foostan/lskbd/pcbs/common/left.kicad_sch

## KiCad design pcbs/common/left.kicad_sch (2024-03-01)

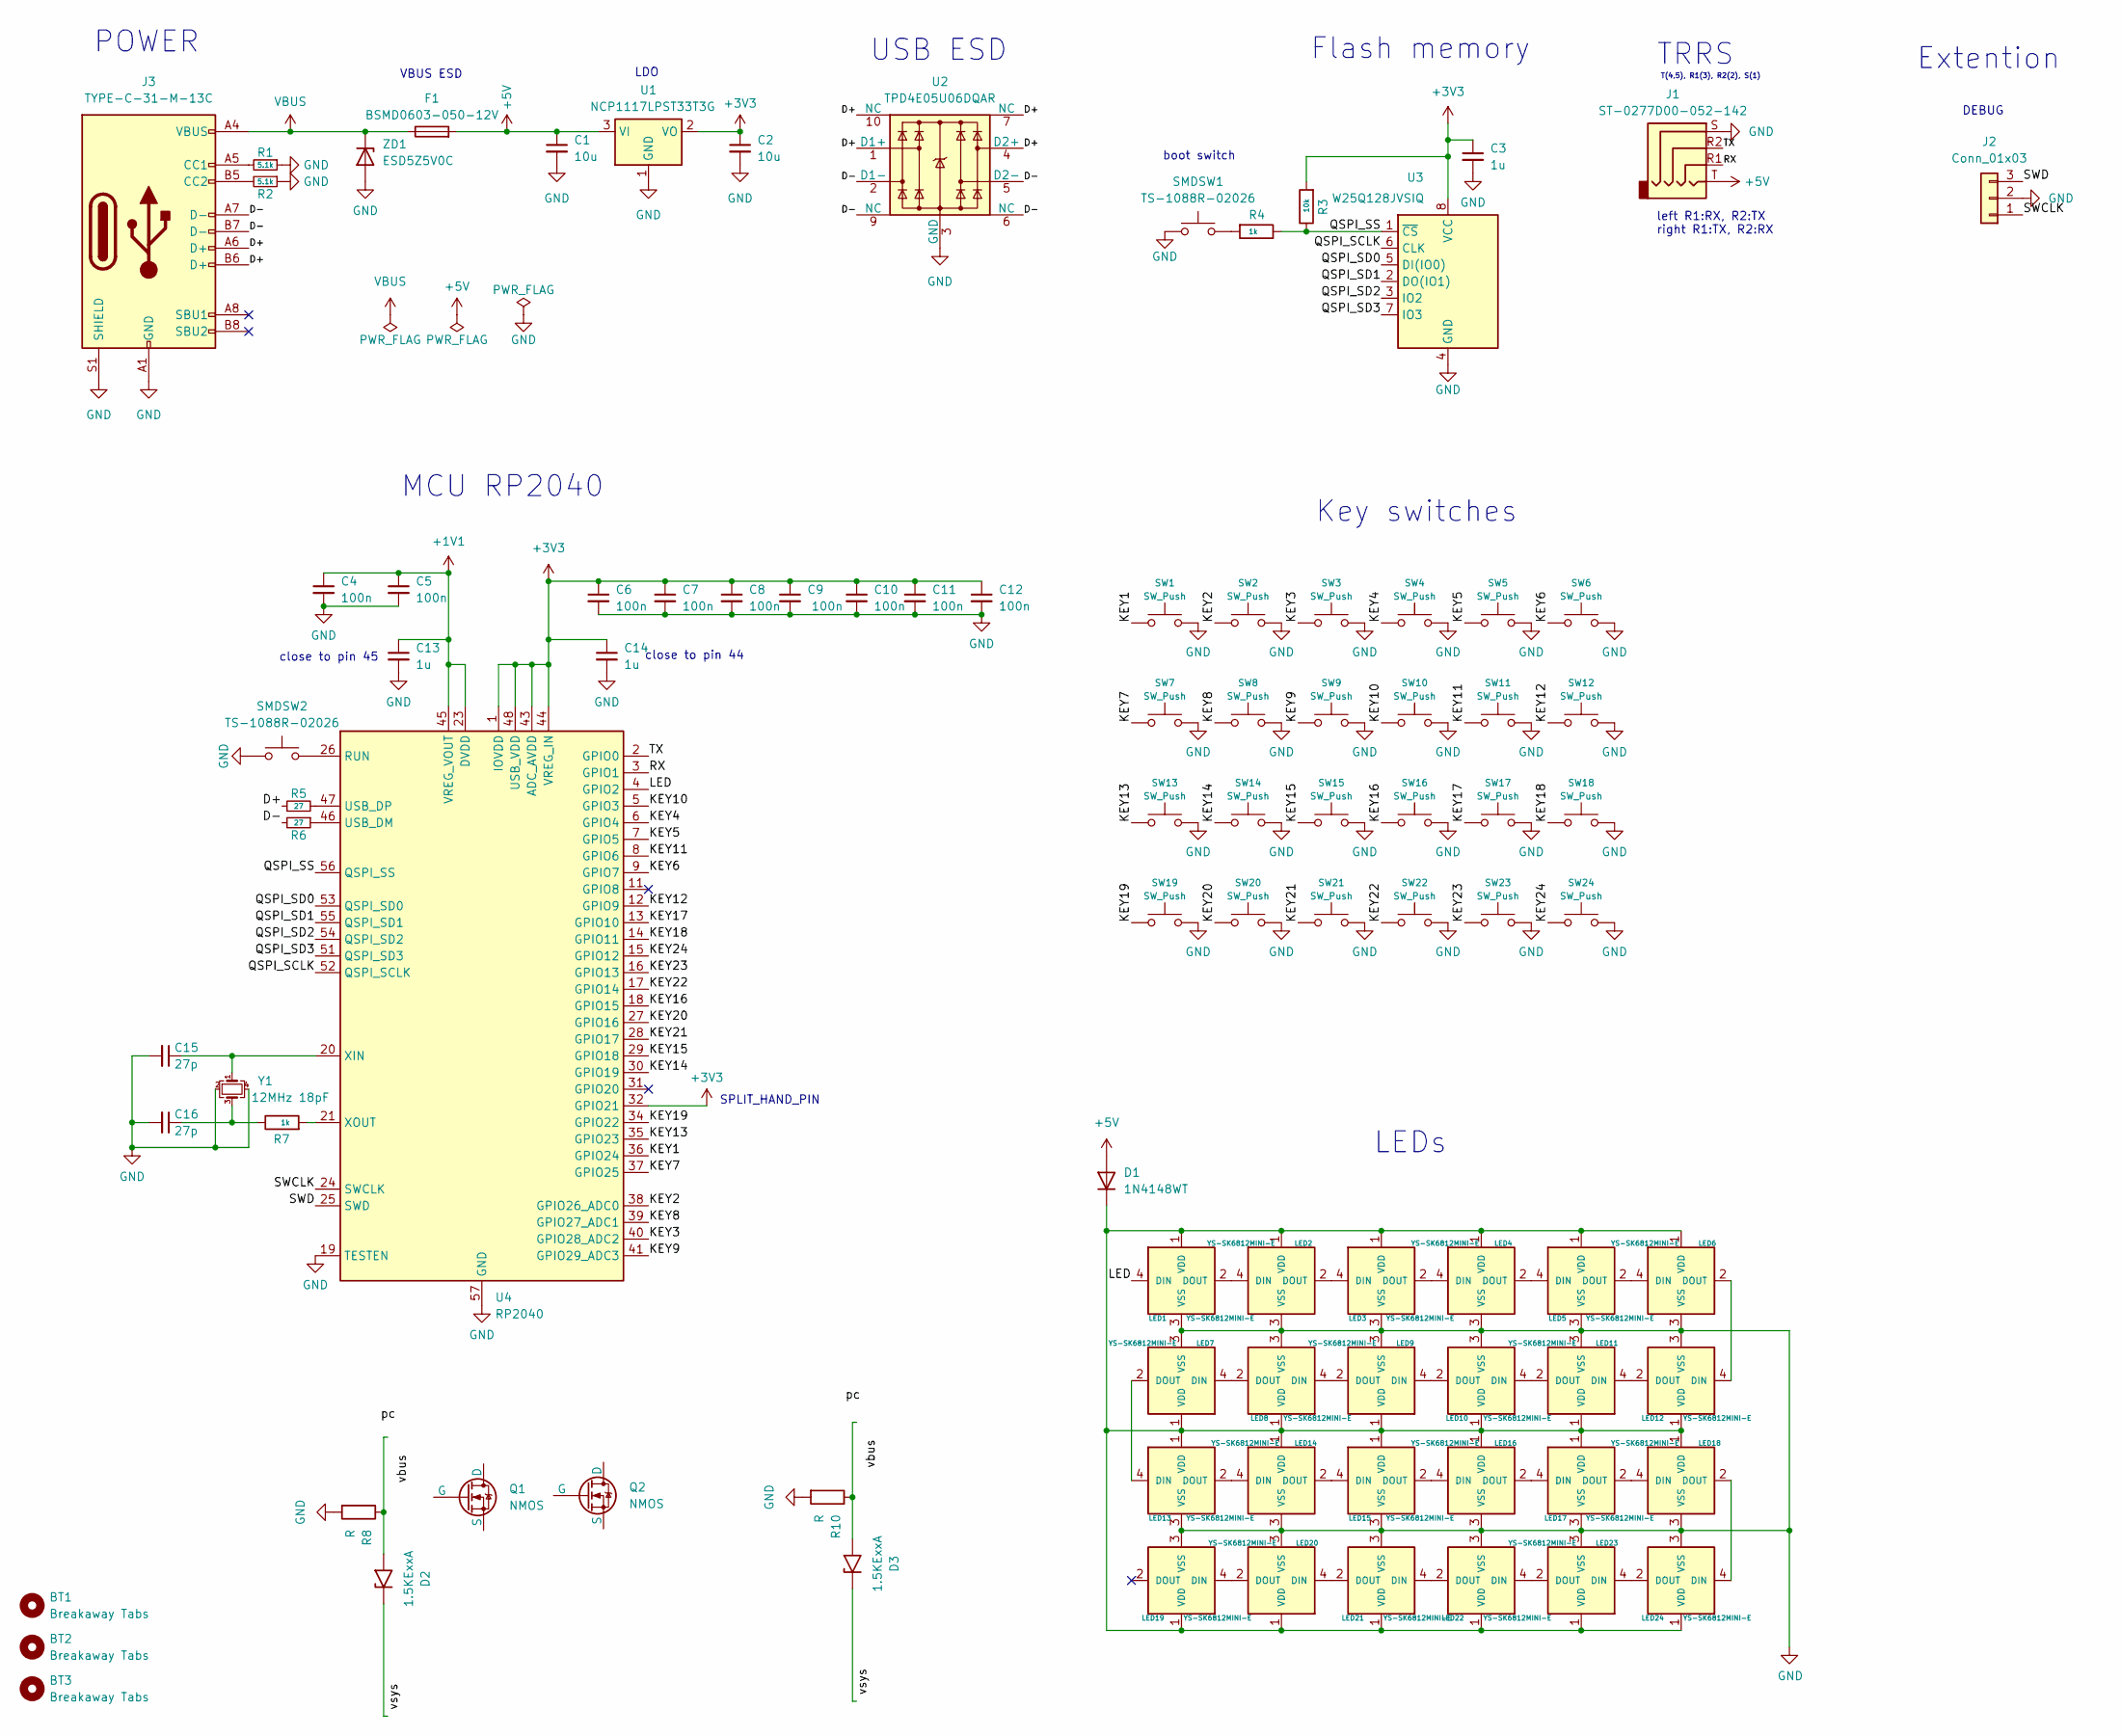
[picture p5: schematic left.kicad_sch]

Parts:
BT1, BT2, BT3: Breakaway Tabs; Breakaway_Tabs
C1, C2: 10u; C_0402_1005Metric
C3, C13, C14: 1u; C_0402_1005Metric
C4, C5, C6, C7, C8, C9, C10, C11, C12: 100n; C_0402_1005Metric
C15, C16: 27p; C_0402_1005Metric
D1: 1N4148WT; D_SOD-523; JLCPCB Part # C232841
D2, D3: 1.5KExxA; D_DO-201AE_P15.24mm_Horizontal
F1: BSMD0603-050-12V; Fuse_0603_1608Metric; JLCPCB Part # C2844464
J1: ST-0277D00-052-142; JLCPCB Part # C2837093
J2: Conn_01x03; PinHeader_1x03_P2.54mm_Vertical
J3: TYPE-C-31-M-13C; JLCPCB Part # C2848620
LED1, LED2, LED3, LED4, LED5, LED6, LED7, LED8, LED9, LED10, LED11, LED12, LED13, LED14, LED15, LED16, LED17, LED18, LED19, LED20, LED21, LED22, LED23, LED24: YS-SK6812MINI-E
Q1, Q2: NMOS
R1, R2: 5.1k; R_0402_1005Metric
R3: 10k; R_0402_1005Metric
R4, R7: 1k; R_0402_1005Metric
R5, R6: 27; R_0402_1005Metric
R8, R10: R
SMDSW1, SMDSW2: TS-1088R-02026; JLCPCB Part # C455280
SW1, SW2, SW3, SW4, SW5, SW6, SW7, SW8, SW9, SW10, SW11, SW12, SW13, SW14, SW15, SW16, SW17, SW18, SW19, SW20, SW21, SW22, SW23, SW24: SW_Push; keyswitch_choc12_hotswap_1u
U1: NCP1117LPST33T3G; SOT-223-3_TabPin2; JLCPCB Part # C146799
U2: TPD4E05U06DQAR; USON-10_2.5x1.0mm_P0.5mm; JLCPCB Part # C138714
U3: W25Q128JVSIQ; SOIC-8_5.23x5.23mm_P1.27mm; JLCPCB Part # C113767
U4: RP2040; QFN-56-1EP_7x7mm_P0.4mm_EP3.2x3.2mm; JLCPCB Part # C2040
Y1: 12MHz 18pF; Crystal_SMD_3225-4Pin_3.2x2.5mm; MFR.Part # Q22FA23V0041800; JLCPCB Part # C91749
ZD1: ESD5Z5V0C; D_SOD-523; JLCPCB Part # C2901325

Connections:
+1V1: C4.1, C5.1, C13.1, U4.23 (DVDD), U4.45 (VREG_VOUT), U4.50 (DVDD)
+3V3: C2.1, C3.1, C6.1, C7.1, C8.1, C9.1, C10.1, C11.1, C12.1, C14.1, R3.2, U1.2 (VO), U3.8 (VCC), U4.1 (IOVDD), U4.10 (IOVDD), U4.22 (IOVDD), U4.32 (GPIO21), U4.33 (IOVDD), U4.42 (IOVDD), U4.43 (ADC_AVDD), U4.44 (VREG_IN), U4.48 (USB_VDD), U4.49 (IOVDD)
+5V: C1.1, D1.2 (A), F1.2, J1.T, U1.3 (VI)
D+: J3.A6 (D+), J3.B6 (D+), R5.1, U2.1 (D1+), U2.4 (D2+), U2.7 (NC), U2.10 (NC)
D-: J3.A7 (D-), J3.B7 (D-), R6.2, U2.2 (D1-), U2.5 (D2-), U2.6 (NC), U2.9 (NC)
GND: C1.2, C2.2, C3.2, C4.2, C5.2, C6.2, C7.2, C8.2, C9.2, C10.2, C11.2, C12.2, C13.2, C14.2, C15.2, C16.2, J1.S, J2.2, J3.A1 (GND), J3.A12 (GND), J3.B1 (GND), J3.B12 (GND), J3.S1 (SHIELD), LED1.3 (VSS), LED2.3 (VSS), LED3.3 (VSS), LED4.3 (VSS), LED5.3 (VSS), LED6.3 (VSS), LED7.3 (VSS), LED8.3 (VSS), LED9.3 (VSS), LED10.3 (VSS), LED11.3 (VSS), LED12.3 (VSS), LED13.3 (VSS), LED14.3 (VSS), LED15.3 (VSS), LED16.3 (VSS), LED17.3 (VSS), LED18.3 (VSS), LED19.3 (VSS), LED20.3 (VSS), LED21.3 (VSS), LED22.3 (VSS), LED23.3 (VSS), LED24.3 (VSS), R1.1, R2.1, R8.2, R10.2, SMDSW1.1, SMDSW2.1, SW1.2, SW2.2, SW3.2, SW4.2, SW5.2, SW6.2, SW7.2, SW8.2, SW9.2, SW10.2, SW11.2, SW12.2, SW13.2, SW14.2, SW15.2, SW16.2, SW17.2, SW18.2, SW19.2, SW20.2, SW21.2, SW22.2, SW23.2, SW24.2, U1.1 (GND), U2.3 (GND), U2.8 (GND), U3.4 (GND), U4.19 (TESTEN), U4.57 (GND), Y1.2, Y1.4, ZD1.2 (A)
KEY1: SW1.1, U4.36 (GPIO24)
KEY2: SW2.1, U4.38 (GPIO26_ADC0)
KEY3: SW3.1, U4.40 (GPIO28_ADC2)
KEY4: SW4.1, U4.6 (GPIO4)
KEY5: SW5.1, U4.7 (GPIO5)
KEY6: SW6.1, U4.9 (GPIO7)
KEY7: SW7.1, U4.37 (GPIO25)
KEY8: SW8.1, U4.39 (GPIO27_ADC1)
KEY9: SW9.1, U4.41 (GPIO29_ADC3)
KEY10: SW10.1, U4.5 (GPIO3)
KEY11: SW11.1, U4.8 (GPIO6)
KEY12: SW12.1, U4.12 (GPIO9)
KEY13: SW13.1, U4.35 (GPIO23)
KEY14: SW14.1, U4.30 (GPIO19)
KEY15: SW15.1, U4.29 (GPIO18)
KEY16: SW16.1, U4.18 (GPIO15)
KEY17: SW17.1, U4.13 (GPIO10)
KEY18: SW18.1, U4.14 (GPIO11)
KEY19: SW19.1, U4.34 (GPIO22)
KEY20: SW20.1, U4.27 (GPIO16)
KEY21: SW21.1, U4.28 (GPIO17)
KEY22: SW22.1, U4.17 (GPIO14)
KEY23: SW23.1, U4.16 (GPIO13)
KEY24: SW24.1, U4.15 (GPIO12)
LED: LED1.4 (DIN), U4.4 (GPIO2)
unnamed: C15.1, U4.20 (XIN), Y1.1
unnamed: C16.1, R7.1, Y1.3
unnamed: D1.1 (K), LED1.1 (VDD), LED2.1 (VDD), LED3.1 (VDD), LED4.1 (VDD), LED5.1 (VDD), LED6.1 (VDD), LED7.1 (VDD), LED8.1 (VDD), LED9.1 (VDD), LED10.1 (VDD), LED11.1 (VDD), LED12.1 (VDD), LED13.1 (VDD), LED14.1 (VDD), LED15.1 (VDD), LED16.1 (VDD), LED17.1 (VDD), LED18.1 (VDD), LED19.1 (VDD), LED20.1 (VDD), LED21.1 (VDD), LED22.1 (VDD), LED23.1 (VDD), LED24.1 (VDD)
unnamed: D2.2 (A2), R8.1
unnamed: D3.2 (A2), R10.1
unnamed: J3.A5 (CC1), R1.2
unnamed: J3.B5 (CC2), R2.2
unnamed: LED1.2 (DOUT), LED2.4 (DIN)
unnamed: LED2.2 (DOUT), LED3.4 (DIN)
unnamed: LED3.2 (DOUT), LED4.4 (DIN)
unnamed: LED4.2 (DOUT), LED5.4 (DIN)
unnamed: LED5.2 (DOUT), LED6.4 (DIN)
unnamed: LED7.4 (DIN), LED8.2 (DOUT)
unnamed: LED8.4 (DIN), LED9.2 (DOUT)
unnamed: LED9.4 (DIN), LED10.2 (DOUT)
unnamed: LED10.4 (DIN), LED11.2 (DOUT)
unnamed: LED11.4 (DIN), LED12.2 (DOUT)
unnamed: LED6.2 (DOUT), LED12.4 (DIN)
unnamed: LED13.2 (DOUT), LED14.4 (DIN)
unnamed: LED7.2 (DOUT), LED13.4 (DIN)
unnamed: LED14.2 (DOUT), LED15.4 (DIN)
unnamed: LED15.2 (DOUT), LED16.4 (DIN)
unnamed: LED16.2 (DOUT), LED17.4 (DIN)
unnamed: LED17.2 (DOUT), LED18.4 (DIN)
unnamed: LED18.2 (DOUT), LED24.4 (DIN)
unnamed: LED19.4 (DIN), LED20.2 (DOUT)
unnamed: LED20.4 (DIN), LED21.2 (DOUT)
unnamed: LED21.4 (DIN), LED22.2 (DOUT)
unnamed: LED22.4 (DIN), LED23.2 (DOUT)
unnamed: LED23.4 (DIN), LED24.2 (DOUT)
unnamed: R4.2, SMDSW1.2
unnamed: R5.2, U4.47 (USB_DP)
unnamed: R6.1, U4.46 (USB_DM)
unnamed: R7.2, U4.21 (XOUT)
unnamed: SMDSW2.2, U4.26 (RUN)
QSPI_SCLK: U3.6 (CLK), U4.52 (QSPI_SCLK)
QSPI_SD0: U3.5 (DI(IO0)), U4.53 (QSPI_SD0)
QSPI_SD1: U3.2 (DO(IO1)), U4.55 (QSPI_SD1)
QSPI_SD2: U3.3 (IO2), U4.54 (QSPI_SD2)
QSPI_SD3: U3.7 (IO3), U4.51 (QSPI_SD3)
QSPI_SS: R3.1, R4.1, U3.1 (~CS), U4.56 (QSPI_SS)
RX: J1.R1, U4.3 (GPIO1)
SWCLK: J2.1, U4.24 (SWCLK)
SWD: J2.3, U4.25 (SWD)
TX: J1.R2, U4.2 (GPIO0)
vbus: F1.1, J3.A4 (VBUS), J3.A9 (VBUS), J3.B4 (VBUS), J3.B9 (VBUS), ZD1.1 (K)

Notes on the sheet:
MCU RP2040
Key switches
close to pin 45
DEBUG
USB ESD
LDO
Flash memory
POWER
LEDs
left R1:RX, R2:TX right R1:TX, R2:RX
Extention
TRRS
T(4,5), R1(3), R2(2), S(1)
VBUS ESD
SPLIT_HAND_PIN
boot switch
close to pin 44
