foostan/lskbd/pcbs/common/right.kicad_sch

## KiCad design pcbs/common/right.kicad_sch (2024-01-26)

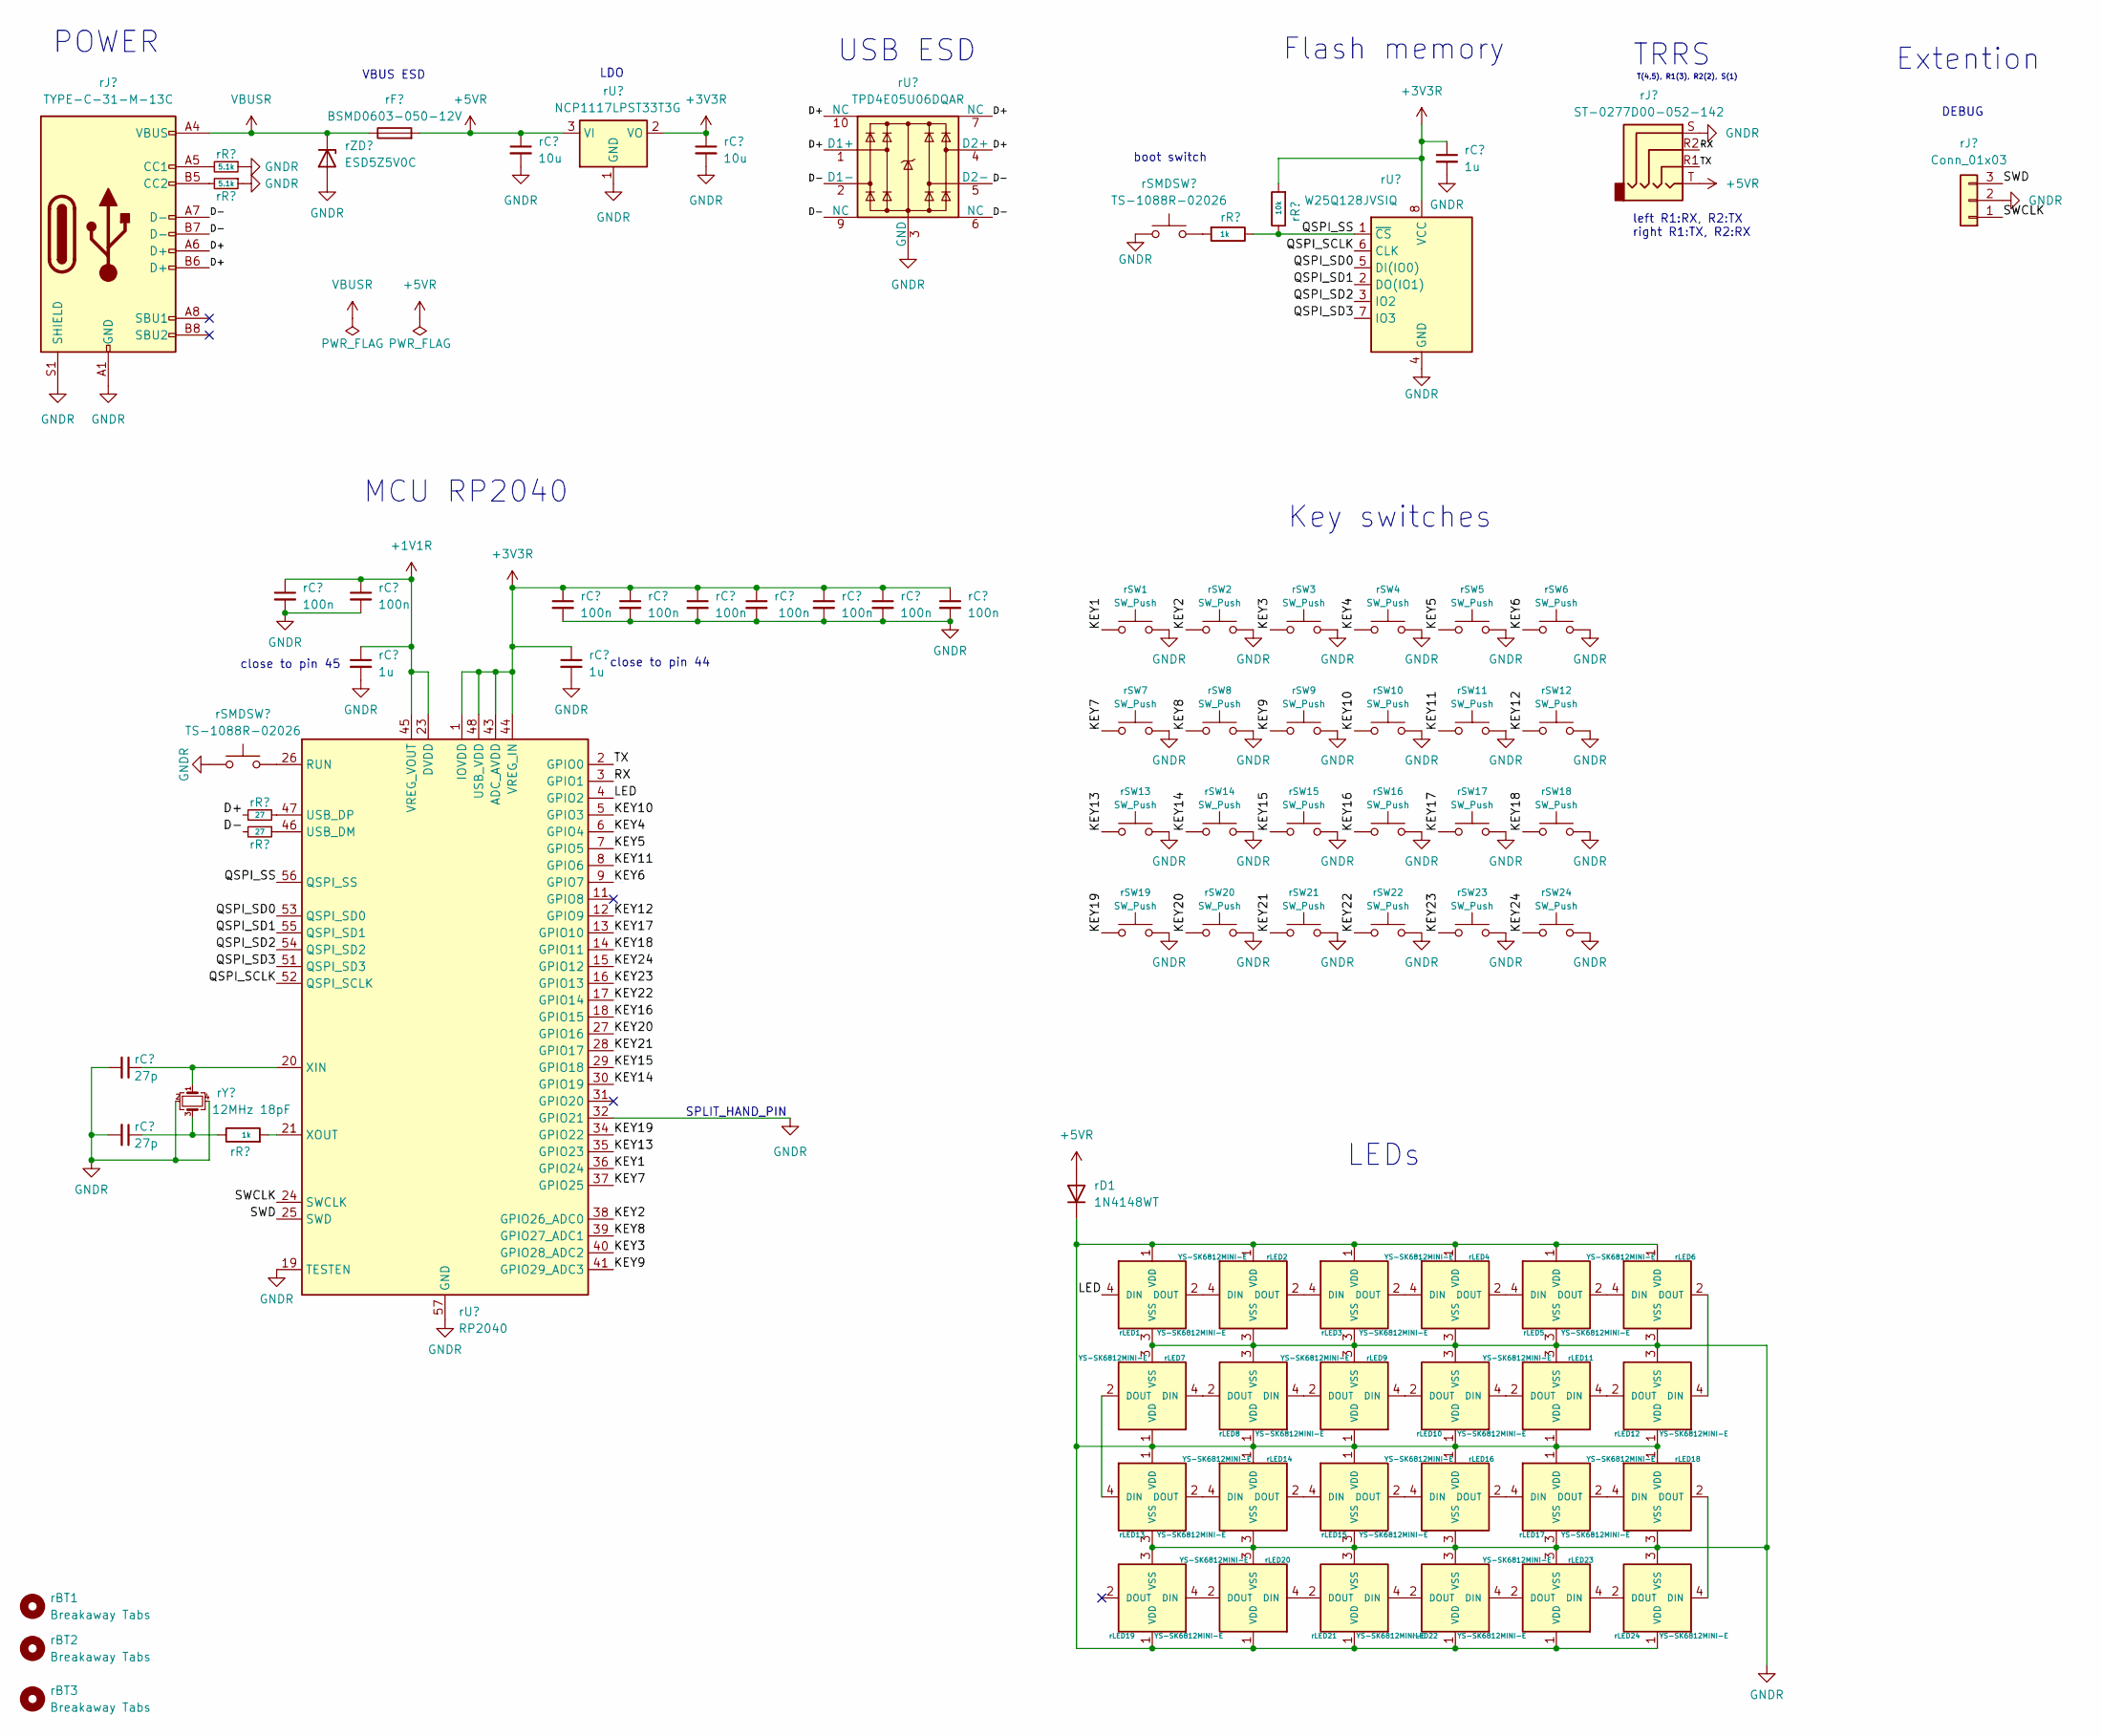
[picture p6: schematic right.kicad_sch]

Parts:
rBT1, rBT2, rBT3: Breakaway Tabs; Breakaway_Tabs
rC1, rC2: 10u; C_0402_1005Metric
rC3, rC13, rC14: 1u; C_0402_1005Metric
rC4, rC5, rC6, rC7, rC8, rC9, rC10, rC11, rC12: 100n; C_0402_1005Metric
rC15, rC16: 27p; C_0402_1005Metric
rD1: 1N4148WT; D_SOD-523; JLCPCB Part # C232841
rF1: BSMD0603-050-12V; Fuse_0603_1608Metric; JLCPCB Part # C2844464
rJ1: ST-0277D00-052-142; JLCPCB Part # C2837093
rJ2: Conn_01x03; PinHeader_1x03_P2.54mm_Vertical
rJ3: TYPE-C-31-M-13C; JLCPCB Part # C2848620
rLED1, rLED2, rLED3, rLED4, rLED5, rLED6, rLED7, rLED8, rLED9, rLED10, rLED11, rLED12, rLED13, rLED14, rLED15, rLED16, rLED17, rLED18, rLED19, rLED20, rLED21, rLED22, rLED23, rLED24: YS-SK6812MINI-E
rR1, rR2: 5.1k; R_0402_1005Metric
rR3: 10k; R_0402_1005Metric
rR4, rR7: 1k; R_0402_1005Metric
rR5, rR6: 27; R_0402_1005Metric
rSMDSW1, rSMDSW2: TS-1088R-02026; JLCPCB Part # C455280
rSW1, rSW2, rSW3, rSW4, rSW5, rSW6, rSW7, rSW8, rSW9, rSW10, rSW11, rSW12, rSW13, rSW14, rSW15, rSW16, rSW17, rSW18, rSW19, rSW20, rSW21, rSW22, rSW23, rSW24: SW_Push; keyswitch_choc12_hotswap_1u
rU1: NCP1117LPST33T3G; SOT-223-3_TabPin2; JLCPCB Part # C146799
rU2: TPD4E05U06DQAR; USON-10_2.5x1.0mm_P0.5mm; JLCPCB Part # C138714
rU3: W25Q128JVSIQ; SOIC-8_5.23x5.23mm_P1.27mm; JLCPCB Part # C113767
rU4: RP2040; QFN-56-1EP_7x7mm_P0.4mm_EP3.2x3.2mm; JLCPCB Part # C2040
rY1: 12MHz 18pF; Crystal_SMD_3225-4Pin_3.2x2.5mm; MFR.Part # Q22FA23V0041800; JLCPCB Part # C91749
rZD1: ESD5Z5V0C; D_SOD-523; JLCPCB Part # C2901325

Connections:
+1V1R: rC4.1, rC5.1, rC13.1, rU4.23 (DVDD), rU4.45 (VREG_VOUT), rU4.50 (DVDD)
+3V3R: rC2.1, rC3.1, rC6.1, rC7.1, rC8.1, rC9.1, rC10.1, rC11.1, rC12.1, rC14.1, rR3.2, rU1.2 (VO), rU3.8 (VCC), rU4.1 (IOVDD), rU4.10 (IOVDD), rU4.22 (IOVDD), rU4.33 (IOVDD), rU4.42 (IOVDD), rU4.43 (ADC_AVDD), rU4.44 (VREG_IN), rU4.48 (USB_VDD), rU4.49 (IOVDD)
+5VR: rC1.1, rD1.2 (A), rF1.2, rJ1.T, rU1.3 (VI)
D+: rJ3.A6 (D+), rJ3.B6 (D+), rR5.1, rU2.1 (D1+), rU2.4 (D2+), rU2.7 (NC), rU2.10 (NC)
D-: rJ3.A7 (D-), rJ3.B7 (D-), rR6.2, rU2.2 (D1-), rU2.5 (D2-), rU2.6 (NC), rU2.9 (NC)
GNDR: rC1.2, rC2.2, rC3.2, rC4.2, rC5.2, rC6.2, rC7.2, rC8.2, rC9.2, rC10.2, rC11.2, rC12.2, rC13.2, rC14.2, rC15.2, rC16.2, rJ1.S, rJ2.2, rJ3.A1 (GND), rJ3.A12 (GND), rJ3.B1 (GND), rJ3.B12 (GND), rJ3.S1 (SHIELD), rLED1.3 (VSS), rLED2.3 (VSS), rLED3.3 (VSS), rLED4.3 (VSS), rLED5.3 (VSS), rLED6.3 (VSS), rLED7.3 (VSS), rLED8.3 (VSS), rLED9.3 (VSS), rLED10.3 (VSS), rLED11.3 (VSS), rLED12.3 (VSS), rLED13.3 (VSS), rLED14.3 (VSS), rLED15.3 (VSS), rLED16.3 (VSS), rLED17.3 (VSS), rLED18.3 (VSS), rLED19.3 (VSS), rLED20.3 (VSS), rLED21.3 (VSS), rLED22.3 (VSS), rLED23.3 (VSS), rLED24.3 (VSS), rR1.1, rR2.1, rSMDSW1.1, rSMDSW2.1, rSW1.2, rSW2.2, rSW3.2, rSW4.2, rSW5.2, rSW6.2, rSW7.2, rSW8.2, rSW9.2, rSW10.2, rSW11.2, rSW12.2, rSW13.2, rSW14.2, rSW15.2, rSW16.2, rSW17.2, rSW18.2, rSW19.2, rSW20.2, rSW21.2, rSW22.2, rSW23.2, rSW24.2, rU1.1 (GND), rU2.3 (GND), rU2.8 (GND), rU3.4 (GND), rU4.19 (TESTEN), rU4.32 (GPIO21), rU4.57 (GND), rY1.2, rY1.4, rZD1.2 (A)
KEY1: rSW1.1, rU4.36 (GPIO24)
KEY2: rSW2.1, rU4.38 (GPIO26_ADC0)
KEY3: rSW3.1, rU4.40 (GPIO28_ADC2)
KEY4: rSW4.1, rU4.6 (GPIO4)
KEY5: rSW5.1, rU4.7 (GPIO5)
KEY6: rSW6.1, rU4.9 (GPIO7)
KEY7: rSW7.1, rU4.37 (GPIO25)
KEY8: rSW8.1, rU4.39 (GPIO27_ADC1)
KEY9: rSW9.1, rU4.41 (GPIO29_ADC3)
KEY10: rSW10.1, rU4.5 (GPIO3)
KEY11: rSW11.1, rU4.8 (GPIO6)
KEY12: rSW12.1, rU4.12 (GPIO9)
KEY13: rSW13.1, rU4.35 (GPIO23)
KEY14: rSW14.1, rU4.30 (GPIO19)
KEY15: rSW15.1, rU4.29 (GPIO18)
KEY16: rSW16.1, rU4.18 (GPIO15)
KEY17: rSW17.1, rU4.13 (GPIO10)
KEY18: rSW18.1, rU4.14 (GPIO11)
KEY19: rSW19.1, rU4.34 (GPIO22)
KEY20: rSW20.1, rU4.27 (GPIO16)
KEY21: rSW21.1, rU4.28 (GPIO17)
KEY22: rSW22.1, rU4.17 (GPIO14)
KEY23: rSW23.1, rU4.16 (GPIO13)
KEY24: rSW24.1, rU4.15 (GPIO12)
LED: rLED1.4 (DIN), rU4.4 (GPIO2)
unnamed: rC15.1, rU4.20 (XIN), rY1.1
unnamed: rC16.1, rR7.1, rY1.3
unnamed: rD1.1 (K), rLED1.1 (VDD), rLED2.1 (VDD), rLED3.1 (VDD), rLED4.1 (VDD), rLED5.1 (VDD), rLED6.1 (VDD), rLED7.1 (VDD), rLED8.1 (VDD), rLED9.1 (VDD), rLED10.1 (VDD), rLED11.1 (VDD), rLED12.1 (VDD), rLED13.1 (VDD), rLED14.1 (VDD), rLED15.1 (VDD), rLED16.1 (VDD), rLED17.1 (VDD), rLED18.1 (VDD), rLED19.1 (VDD), rLED20.1 (VDD), rLED21.1 (VDD), rLED22.1 (VDD), rLED23.1 (VDD), rLED24.1 (VDD)
unnamed: rJ3.A5 (CC1), rR1.2
unnamed: rJ3.B5 (CC2), rR2.2
unnamed: rLED1.2 (DOUT), rLED2.4 (DIN)
unnamed: rLED2.2 (DOUT), rLED3.4 (DIN)
unnamed: rLED3.2 (DOUT), rLED4.4 (DIN)
unnamed: rLED4.2 (DOUT), rLED5.4 (DIN)
unnamed: rLED5.2 (DOUT), rLED6.4 (DIN)
unnamed: rLED7.4 (DIN), rLED8.2 (DOUT)
unnamed: rLED8.4 (DIN), rLED9.2 (DOUT)
unnamed: rLED9.4 (DIN), rLED10.2 (DOUT)
unnamed: rLED10.4 (DIN), rLED11.2 (DOUT)
unnamed: rLED11.4 (DIN), rLED12.2 (DOUT)
unnamed: rLED6.2 (DOUT), rLED12.4 (DIN)
unnamed: rLED13.2 (DOUT), rLED14.4 (DIN)
unnamed: rLED7.2 (DOUT), rLED13.4 (DIN)
unnamed: rLED14.2 (DOUT), rLED15.4 (DIN)
unnamed: rLED15.2 (DOUT), rLED16.4 (DIN)
unnamed: rLED16.2 (DOUT), rLED17.4 (DIN)
unnamed: rLED17.2 (DOUT), rLED18.4 (DIN)
unnamed: rLED18.2 (DOUT), rLED24.4 (DIN)
unnamed: rLED19.4 (DIN), rLED20.2 (DOUT)
unnamed: rLED20.4 (DIN), rLED21.2 (DOUT)
unnamed: rLED21.4 (DIN), rLED22.2 (DOUT)
unnamed: rLED22.4 (DIN), rLED23.2 (DOUT)
unnamed: rLED23.4 (DIN), rLED24.2 (DOUT)
unnamed: rR4.2, rSMDSW1.2
unnamed: rR5.2, rU4.47 (USB_DP)
unnamed: rR6.1, rU4.46 (USB_DM)
unnamed: rR7.2, rU4.21 (XOUT)
unnamed: rSMDSW2.2, rU4.26 (RUN)
QSPI_SCLK: rU3.6 (CLK), rU4.52 (QSPI_SCLK)
QSPI_SD0: rU3.5 (DI(IO0)), rU4.53 (QSPI_SD0)
QSPI_SD1: rU3.2 (DO(IO1)), rU4.55 (QSPI_SD1)
QSPI_SD2: rU3.3 (IO2), rU4.54 (QSPI_SD2)
QSPI_SD3: rU3.7 (IO3), rU4.51 (QSPI_SD3)
QSPI_SS: rR3.1, rR4.1, rU3.1 (~CS), rU4.56 (QSPI_SS)
RX: rJ1.R2, rU4.3 (GPIO1)
SWCLK: rJ2.1, rU4.24 (SWCLK)
SWD: rJ2.3, rU4.25 (SWD)
TX: rJ1.R1, rU4.2 (GPIO0)
VBUSR: rF1.1, rJ3.A4 (VBUS), rJ3.A9 (VBUS), rJ3.B4 (VBUS), rJ3.B9 (VBUS), rZD1.1 (K)

Notes on the sheet:
USB ESD
LEDs
Flash memory
MCU RP2040
DEBUG
Key switches
POWER
boot switch
LDO
Extention
TRRS
close to pin 45
close to pin 44
left R1:RX, R2:TX right R1:TX, R2:RX
SPLIT_HAND_PIN
T(4,5), R1(3), R2(2), S(1)
VBUS ESD
